pdaehne/SNES-LoROM-Cartridge-wo-Save/images/Xgpro_Program_Slot1.png

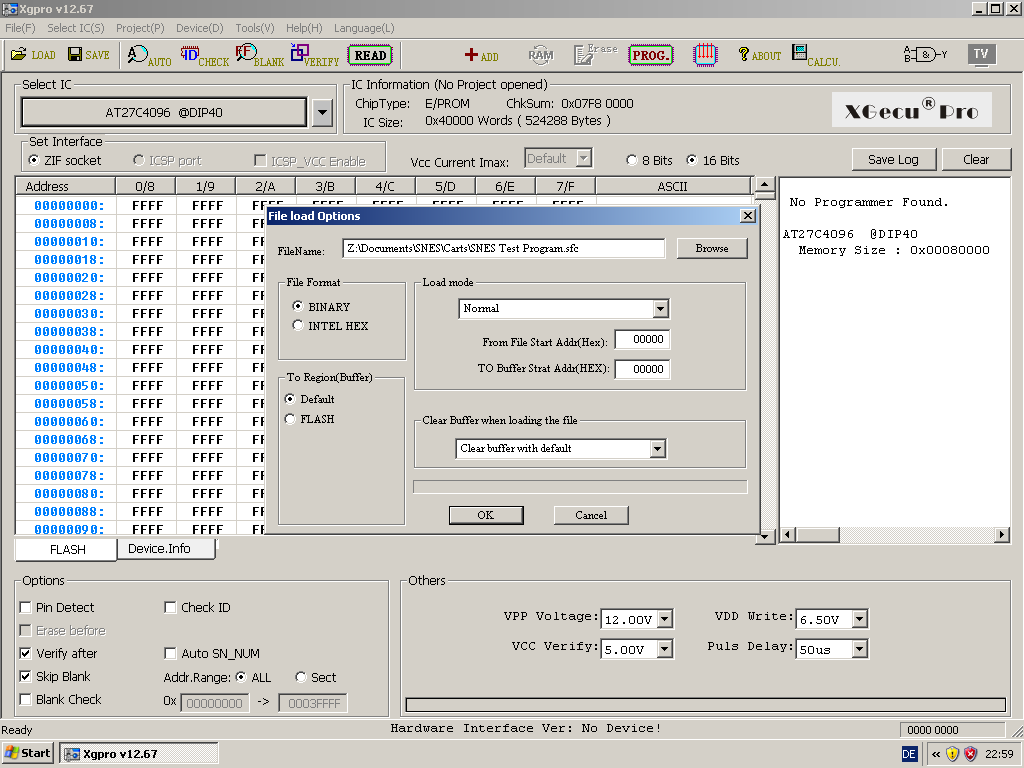
images/Xgpro_Program_Slot1.png
