pdaehne/SNES-LoROM-Cartridge-wo-Save/images/Xgpro_Program_Slot4.png

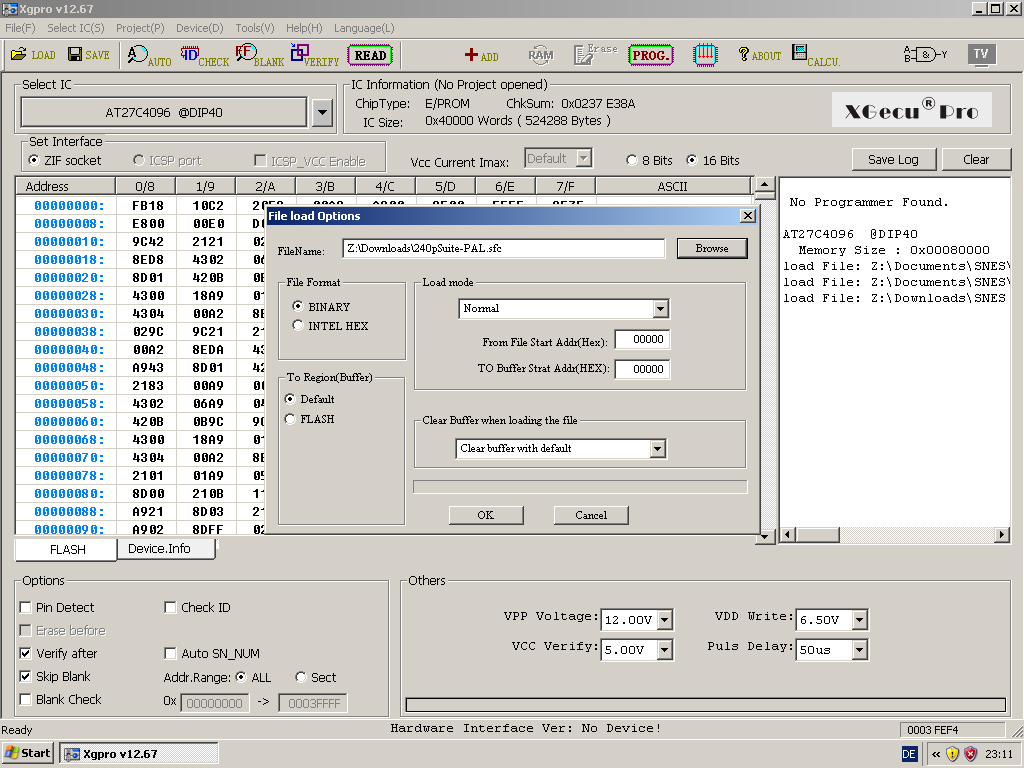
images/Xgpro_Program_Slot4.png
